mihi4/F-16_BMSAITRightAUX/arduino/BMSAIT_RightAuxController/ax1201728sg.h

#ifndef ax1201728sg_h
#define ax1201728sg_h
#include <Arduino.h>

class SwitecX12 {
  public:
    unsigned char pinStep;
    unsigned char pinDir;
    unsigned int currentStep;      // step we are currently at
    unsigned int targetStep;       // target we are moving to
    unsigned int steps;            // total steps available
    unsigned long time0;           // time when we entered this state
    unsigned int microDelay;       // microsecs until next state
    unsigned short (*accelTable)[2]; // accel table can be modified.
    unsigned int maxVel;           // fastest vel allowed
    unsigned int vel;              // steps travelled under acceleration
    int dir;                      // direction -1,0,1
    boolean stopped;               // true if stopped
    SwitecX12(unsigned int steps, unsigned char pinStep, unsigned char pinDir);

    //void stepUp();
    void step(int dir);
    void zero();
    void stepTo(int position);
    void advance();
    void update();
    void setPosition(unsigned int pos);
};

#endif
